RomanBych2019/Display_240x240/data/screen0.png

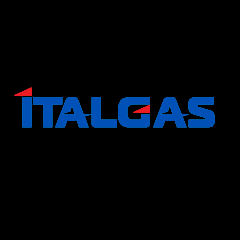
data/screen0.png
