RomanBych2019/Display_240x240/data/screen2.png

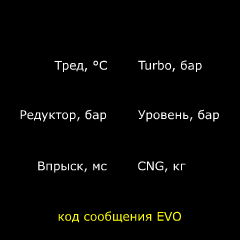
data/screen2.png
