RomanBych2019/Display_240x240/data/screen4.png

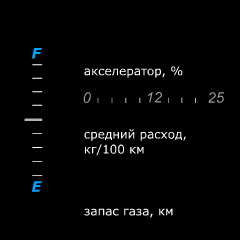
data/screen4.png
