RomanBych2019/Display_240x240/data/screen10.png

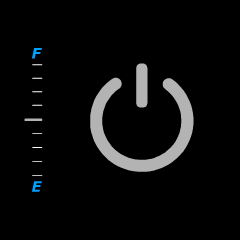
data/screen10.png
