RomanBych2019/Display_240x240/src/can_settings.h

#pragma once
#include <Arduino.h>
#include "set"

struct distanceLPG
{
    float begin;    //  начало отсчета пробега на газовом топливе в поездке
    float result;   //  пробег на газовом топливе в поездке
    float gas_mileage; //  оставшийся пробег на газе
};

struct Can_Data
{
    uint8_t state = 0;           //  Режим дизель - 0, смешанный - 1
    float cngInjectionTime;    //  Время впрыска газа, 0.1 мсек
    float cngIstValue = 0;     //  Мгновенный расход газа, 0.1 кг/час
    uint8_t cngDieselReduction;  //  карта дизель
    float cngTurboPressure;    //  давление турбо
    float cngRailPressure;     //  Давлениев газа в рампе форсунок, 0.02 бар
    int16_t cngRailTemperature;   //  Температура газа в рампе форсунок, 0.1 С -40С
    uint32_t hoursindiesel;      //  Время работы на ДТ, 1 мин
    uint32_t hoursindualfuel;    //  Время работы в смешанном режиме, 1 мин
    uint8_t cngLevel;            //  Давление в балонах,  бар
    uint8_t cngWaterTemperature; //  Температура редуктора, 0.1 С -40С
    float cngTripFuel;        //  Расход газа за поездку, 1 гр
    float cngTotalFuelUsed;   //  Общий расход газа, 0.5 кг
    uint8_t ACC;                 //  Педаль акселератора, %
    uint16_t tankVolume = 150;   //  Объем баллонов, м3 (из файла настройки)
    uint8_t errorEVO[6];         //  Ошибки EVO
    uint8_t verID;               //  Version ID High
    uint8_t verFMlow;            //  Version FW Low

    uint32_t rpm = 0;           //  Обороты двигателя
    float wheelSpeed = 0;       //  Скорость автомобиля
    float oilFuelRate = 0;      //  Мгновенный расход ДТ литр/час
    float engineLoad = 0;       //  нагрузка двигатель
    bool cruise = 0;            //  круиз - вкл - 1, выкл - 0
    float distance = 0;         //  пробег автомобиля, метр
    int32_t airTemper;          //  температура воздуха
    int32_t oilTemper;          //  температура масла
    int32_t engineTemper;       //  температура двигателя
    int32_t fuelTemper;         //  температура топлива
    int32_t exhaustGasTemper;   //  температура выхлопных газов
    float vehicleWeight;      //  вес автомобиля

    int16_t lls = 0;            //  уровень ДУТа в литрах
    int16_t full_tank = 100;    //  объем бака в литрах

    String vehicleType{};       // тип автомобиля
    uint16_t canSpeed{};        // скорость can-шины

    uint8_t levelEconomicalDriving; //  уровень экономичного вождения (0-100%)
    // uint32_t travelDistance;
    distanceLPG distLPG;
    float average_gasconsumption; //  средний расход газа на 100 км
};

static const uint32_t PGN1 = 0x18FFF0BB;  // газ
static const uint32_t PGN2 = 0x18FFF1BB;  // газ
static const uint32_t PGN3 = 0x18FFFBBB;  // газ - ошибки
static const uint32_t PGN4 = 0x18FFF8BB;  // газ

static const uint16_t PGN5 = 0xFEF1;  // скорость, круиз-контроль,
static const uint16_t PGN6 = 0xFEC1;  // пробег авто в J1939
static const uint16_t PGN7 = 0xFEF2;  // мгновенный расход ДТ авто в J1939
static const uint16_t PGN8 = 0xF004;  // нагрузка на двигатель в J1939, RPM в J1939
static const uint16_t PGN10 = 0xFEF6; // температура воздуха, выхлопных газов в J1939
static const uint16_t PGN11 = 0xFEEE; // температура ОЖ, масла, топлива в J1939
static const uint16_t PGN12 = 0xFEEA; // вес в J1939

static const uint32_t PGN9 = 0x0CFEC100;  // пробег авто в SHAKMAN
static const uint32_t PGN13 = 0x18FFFAA1UL;             // входящее CAN сообщение о статусе и токе потребления соленоидов
static const uint32_t PGN14 = 0x18FFFBA1UL;             // входящее CAN сообщение об уровне дизельного топлива
static const uint32_t PGN_SEND_ON_EVO = 0x18FFEEDD;     // отправка нажатия кнопки включения/выключения газа
static const uint32_t PGN_SEND_DATA = 0x18FFFEDD;       // отправка диагностической информации для мониторинга


// const std::set<uint32_t> FILTR_ID32{PGN1, PGN2, PGN3, PGN4, PGN9, PGN13};

// const std::set<uint16_t> FILTR_ID16{PGN5, PGN6, PGN7, PGN8, PGN10, PGN11, PGN12};
